xn--nding-jua/XFBAPE/SAMD/SAMD.h

const char* versionstring = "v3.1.4";
const char compile_date[] = __DATE__ " " __TIME__;

// the following defines will overwrite the standard arduino-defines from https://github.com/arduino/ArduinoCore-samd/blob/84c09b3265e2a8b548a29b141f0c9281b1baf154/variants/mkrvidor4000/variant.h
// this is only nescessary, if SAMD21 should transmit audio-data to FPGA. At the moment only ESP32 transmits audio-data
//#define I2S_INTERFACES_COUNT 1 // SAMD21 has two interfaces
//#define I2S_DEVICE 0 // select if I2S device 0 or 1
//#define I2S_CLOCK_GENERATOR 3 // select the correct clock for I2S-interface
//#define PIN_I2S_SD 21 // pin for SerialData (= A6)
//#define PIN_I2S_SCK 02 // pin for bit-clock (= D2)
//#define PIN_I2S_FS 03 // pin for FrameSelect / Wordclock (= D3)

// configure this software
#define USE_DISPLAY             0      // enables support for SSD1308 display connected to I2C
#define USE_MACKIE_MCU          1      // support for MackieMCU via MIDI
#define USE_ALL_MACKIE_FEATURES 0      // enable support for LED-rings, master-fader and 7-seg.-displays (all not supported by X32)
#define USE_XREMOTE             1      // support for XEdit via Ethernet
#define XREMOTE_DEVICE          "X32"  // XEdit will check this value and display the related picture
#define XREMOTE_FW_VER          "4.13" // XEdit will check this version
#define USE_XTOUCH              1      // support for XTouch via Ethernet
#define XTOUCH_COUNT            2      // number of supported XTouch-Devices
#define XTOUCH_COLOR            7      // color to init the channel: 0=BLACK, 1=RED, 2=GREEN, 3=YELLOW, 4=BLUE, 5=PINK, 6=CYAN, 7=WHITE (add 64 to invert)
#define XTOUCH_COLOR_DMX        3      // color to init the channel: 0=BLACK, 1=RED, 2=GREEN, 3=YELLOW, 4=BLUE, 5=PINK, 6=CYAN, 7=WHITE (add 64 to invert)

// includes for FPGA
#include <wiring_private.h>
#include "jtag.h"
#include "fpga.h"
#include <Ethernet.h>
#if USE_XTOUCH == 1
  #include <EthernetUdp.h>
#endif
#include <SPI.h>
#include "Ticker.h"

#if USE_MACKIE_MCU == 1
  #include <MIDI.h>
#endif

// definitions for I2C EEPROM
#include "Wire.h"
#include "I2C_eeprom.h"
#define EEPROM_Address 0x50

/*
Arduino SAMD21 SERCOM usage:
SERCOM0: I2C      <- Display
SERCOM1: SPI      <- W5500 Ethernet
SERCOM2: SPI1     <- unused
SERCOM3: Serial2  <- NINA
SERCOM4: unused (Pins 4/5)
SERCOM5: unused (Pins 16/17)

SerialUSB: USB
Serial1:   X32
*/
#define SerialX32 Serial1
#define SerialNina Serial2

// includes for Serial2 to communicate with NINA. As Serial2 is not within the scope of Arduino,
// we have to create it using the SERCOM-system of the SAMD21
#define PIN_SERIAL2_TX       (0ul)                // Pin description number for PIO_SERCOM on D0
#define PIN_SERIAL2_RX       (1ul)                // Pin description number for PIO_SERCOM on D1
#define PAD_SERIAL2_TX       (UART_TX_PAD_0)      // SERCOM pad 0 TX
#define PAD_SERIAL2_RX       (SERCOM_RX_PAD_1)    // SERCOM pad 1 RX
Uart Serial2(&sercom3, PIN_SERIAL2_RX, PIN_SERIAL2_TX, PAD_SERIAL2_RX, PAD_SERIAL2_TX);

#if USE_MACKIE_MCU == 1
  // includes for Serial3 to communicate with MIDI. As Serial3 is not within the scope of Arduino,
  // we have to create it using the SERCOM-system of the SAMD21
  #define PIN_SERIAL3_TX       (4ul)                // Pin description number for PIO_SERCOM
  #define PIN_SERIAL3_RX       (5ul)                // Pin description number for PIO_SERCOM
  #define PAD_SERIAL3_TX       (UART_TX_PAD_2)      // SERCOM pad 2 TX
  #define PAD_SERIAL3_RX       (SERCOM_RX_PAD_3)    // SERCOM pad 3 RX
  Uart Serial3(&sercom4, PIN_SERIAL3_RX, PIN_SERIAL3_TX, PAD_SERIAL3_RX, PAD_SERIAL3_TX);
  MIDI_CREATE_INSTANCE(HardwareSerial, Serial3, MIDI);
#endif

/*
#define PIN_SERIAL4_TX       (16ul)                // Pin description number for PIO_SERCOM
#define PIN_SERIAL4_RX       (17ul)                // Pin description number for PIO_SERCOM
#define PAD_SERIAL4_TX       (UART_TX_PAD_0)      // SERCOM pad 0 TX
#define PAD_SERIAL4_RX       (SERCOM_RX_PAD_1)    // SERCOM pad 1 RX
Uart Serial4(&sercom5, PIN_SERIAL4_RX, PIN_SERIAL4_TX, PAD_SERIAL4_RX, PAD_SERIAL4_TX);
*/

bool passthroughNINA = false;
bool passthroughNINADebug = false;
#define X32_RINGBUF_LEN 32 //longest command seems to be 22 chars
uint8_t x32RingBuffer[X32_RINGBUF_LEN];
uint16_t x32RingBufferPointer = 0;
uint8_t x32AliveCounter = 59; // preload to 5 seconds (for ticker with 85ms)
uint8_t x32StartupCounter = 100; // 10 Sekunden
String x32AliveCommand = "*8BE#";
bool x32Playback = false;
bool x32Debug = false;
uint8_t x32NumberOfCards = 2;
uint8_t x32currentCardSelection = 0;
uint32_t x32CardSize[2] = {31163136, 15581568}; // one 32GB and one 16GB

struct{ // don't change order of struct! Just add variables or replace with same size!!!
  uint16_t Version = 0;
  IPAddress ip;
  IPAddress xtouchip[XTOUCH_COUNT];
} eeprom_config;

struct{
  uint8_t mac[6] = {0xDE, 0xAD, 0xBE, 0xEF, 0xFE, 0xED};
} config;
I2C_eeprom eeprom(EEPROM_Address, I2C_DEVICESIZE_24LC16);

// Ethernet-objects
EthernetServer server(80);
EthernetServer cmdserver(5025);

#if USE_DISPLAY == 1
  #include "Wire.h"

  // includes for display
  #include "Bitmaps.h"
  #include <Adafruit_GFX.h>
  #include <Adafruit_SSD1306.h>
  #define SCREEN_WIDTH 128 // OLED display width, in pixels
  #define SCREEN_HEIGHT 64 // OLED display height, in pixels
  #define OLED_RESET     -1 // Reset pin # (or -1 if sharing Arduino reset pin)
  #define SCREEN_ADDRESS 0x3C // this address does not fit to the address on the PCB!!!
  Adafruit_SSD1306 display(SCREEN_WIDTH, SCREEN_HEIGHT, &Wire, OLED_RESET);
  uint8_t currentDisplayLine = 0;
#endif

String TOC;
uint8_t tocEntries = 3;
uint8_t tocCounter = 0;

struct {
  String title = "Standby...";
  uint8_t currentTrackNumber;
  uint32_t time;
  uint32_t duration;
  uint8_t progress;
  float volumeMain;
  uint8_t balanceMain;
  float volumeSub;
  float volumeCard;
  float volumeBt;
  float volumeCh[32] = {-48.0f, -48.0f, -48.0f, -48.0f, -48.0f, -48.0f, -48.0f, -48.0f, -48.0f, -48.0f, -48.0f, -48.0f, -48.0f, -48.0f, -48.0f, -48.0f, -48.0f, -48.0f, -48.0f, -48.0f, -48.0f, -48.0f, -48.0f, -48.0f, -48.0f, -48.0f, -48.0f, -48.0f, -48.0f, -48.0f, -48.0f, -48.0f};
  uint8_t balanceCh[32] = {50, 50, 50, 50, 50, 50, 50, 50, 50, 50, 50, 50, 50, 50, 50, 50, 50, 50, 50, 50, 50, 50, 50, 50, 50, 50, 50, 50, 50, 50, 50, 50};
  uint8_t vuMeterCh[32];
  uint8_t audioStatusInfo;

  String MainCtrlVersion;
  String FPGAVersion;
}playerinfo;

// some defines for NINA update mode
#define NINA_PIO27 11
#define NINA_RESET_N 31
unsigned long baud = 115200;
int rts = -1;
int dtr = -1;
bool firmwareUpdateMode = false;
uint8_t ledCounter = 10; // 500ms

// general variables
uint32_t refreshCounter = 0;

#if USE_MACKIE_MCU == 1 || USE_XTOUCH == 1
  uint8_t mackieUpdateCounter = 3; // 300ms update-rate
  bool mackieDmxMode = false;

  struct sMackieMCU_Channel{
    uint16_t faderPosition = 0; // 0...16383
    uint8_t encoderValue = 128; // 0..255 -> 0..12
    uint8_t rec = 0; // 0=OFF, 1=FLASHING, 127=ON (function unused at the moment)
    uint8_t solo = 0; // 0=OFF, 1=FLASHING, 127=ON
    uint8_t mute = 0; // 0=OFF, 1=FLASHING, 127=ON
    uint8_t select = 0; // 0=OFF, 1=FLASHING, 127=ON (function unused at the moment)
    String name;
    uint8_t color = XTOUCH_COLOR; // init the color with desired color for audio-channels (dmx-channels are set in setup())
  };

  struct sMackieMCU_ChannelHW{
    uint16_t faderPositionHW = 0; // 0...16383
    bool faderTouched = false;
    bool faderNeedsUpdate = false;
    uint8_t meterLevel; // 0...12 for Mackie, 0..8 for X-Touch
    uint8_t showValueCounter = 0; // show value for x seconds as counter is at 100ms
  };

  struct {
    uint8_t channelOffset = 0; // runs from 0 to 24
    uint16_t channelOffsetDmx = 0; // runs from 0 to 504
    bool forceUpdate = false;
    sMackieMCU_ChannelHW hardwareChannel[8];
    sMackieMCU_ChannelHW hardwareMainfader;
    sMackieMCU_Channel channel[33]; // values for audio-control
    sMackieMCU_Channel channelDmx[513]; // values for DMX-Control
    uint8_t jogDialValue;
    uint8_t jogDialValueDmx;
  }MackieMCU;
#endif

#if USE_XTOUCH == 1
  EthernetUDP XCtlUdp[XTOUCH_COUNT];
  uint8_t XCtl_UpdateCounter = 4;
  uint16_t XCtlWatchdogCounter[XTOUCH_COUNT];

  uint8_t XCtl_Probe[8] = {0xF0, 0x00, 0x20, 0x32, 0x58, 0x54, 0x00, 0xF7};
  uint8_t XCtl_ProbeResponse[8] = {0xF0, 0x00, 0x20, 0x32, 0x58, 0x54, 0x01, 0xF7};
  uint8_t XCtl_ProbeB[18] = {0xF0, 0x00, 0x00, 0x66, 0x58, 0x01, 0x30, 0x31, 0x35, 0x36, 0x34, 0x30, 0x36, 0x36, 0x37, 0x34, 0x30, 0xF7};
  uint8_t XCtl_ProbeC[18] = {0xF0, 0x00, 0x00, 0x66, 0x58, 0x01, 0x30, 0x31, 0x35, 0x36, 0x34, 0x30, 0x36, 0x33, 0x44, 0x35, 0x36, 0xF7};
  uint8_t XCtl_IdlePacket[7] = {0xF0, 0x00, 0x00, 0x66, 0x14, 0x00, 0xF7};

  struct sXCtl{
    IPAddress ip;
    bool online = false;
    uint8_t channelOffset = 0;
    uint16_t channelOffsetDmx = 0; // 0...504
    bool forceUpdate = false;
    sMackieMCU_ChannelHW hardwareChannel[8];
    sMackieMCU_ChannelHW hardwareMainfader;
    bool showNames = true;
    bool dmxMode = false;
    uint8_t jogDialValue = 0;
    uint8_t jogDialValueDmx = 0;
    char segmentDisplay[12];
    uint8_t buttonLightOn[103];
  }XCtl[XTOUCH_COUNT];
#endif

#if USE_XREMOTE == 1
  EthernetUDP xremoteUdp;
  uint8_t xremoteUpdateCounter = 1;
  char xremote_TxMessage[350]; // the largest binary blob will take up to 20+(70+1))*4 bytes = 408 bytes

  typedef union 
  {
      uint32_t u32;
      int32_t s32;
      uint16_t u16[2];
      int16_t s16[2];
      uint8_t u8[4];
      int8_t s8[4];
      float   f;
  }data_32b;

  char xremote_cmd_info[4]   = {'/', 'i', 'n', 'f'};
  char xremote_cmd_xinfo[4]   = {'/', 'x', 'i', 'n'};
  char xremote_cmd_status[4] = {'/', 's', 't', 'a'};
  char xremote_cmd_xremote[4]   = {'/', 'x', 'r', 'e'};
  char xremote_cmd_unsubscribe[4]   = {'/', 'u', 'n', 's'};
  char xremote_cmd_channel[4]   = {'/', 'c', 'h', '/'};
  char xremote_cmd_main[4]   = {'/', 'm', 'a', 'i'};
  char xremote_cmd_stat[4]   = {'/', '-', 's', 't'};
#endif
