xn--nding-jua/XFBAPE/FPGA/vu_meter_32ch.vhd

-- vu-meter
-- (c) 2023 Dr.-Ing. Christian Noeding
-- christian@noeding-online.de
-- Released under GNU General Public License v3
-- Source: https://www.github.com/xn--nding-jua/Audioplayer
--
-- This file converts 24-bit signed audio-data into a 8-bit unsigned VU-meter between -6dBfs and -78dBfs

library IEEE;
use IEEE.STD_LOGIC_1164.ALL;
use ieee.numeric_std.all;

entity vu_meter_32ch is
	port (
		ch1_in		:	in signed(23 downto 0) := (others=>'0');
		ch2_in		:	in signed(23 downto 0) := (others=>'0');
		ch3_in		:	in signed(23 downto 0) := (others=>'0');
		ch4_in		:	in signed(23 downto 0) := (others=>'0');
		ch5_in		:	in signed(23 downto 0) := (others=>'0');
		ch6_in		:	in signed(23 downto 0) := (others=>'0');
		ch7_in		:	in signed(23 downto 0) := (others=>'0');
		ch8_in		:	in signed(23 downto 0) := (others=>'0');
		ch9_in		:	in signed(23 downto 0) := (others=>'0');
		ch10_in		:	in signed(23 downto 0) := (others=>'0');
		ch11_in		:	in signed(23 downto 0) := (others=>'0');
		ch12_in		:	in signed(23 downto 0) := (others=>'0');
		ch13_in		:	in signed(23 downto 0) := (others=>'0');
		ch14_in		:	in signed(23 downto 0) := (others=>'0');
		ch15_in		:	in signed(23 downto 0) := (others=>'0');
		ch16_in		:	in signed(23 downto 0) := (others=>'0');
		ch17_in		:	in signed(23 downto 0) := (others=>'0');
		ch18_in		:	in signed(23 downto 0) := (others=>'0');
		ch19_in		:	in signed(23 downto 0) := (others=>'0');
		ch20_in		:	in signed(23 downto 0) := (others=>'0');
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
			vu_ch15 <= ch15(20) & ch15(17) & ch15(15) & ch15(13) & ch15(12) & ch15(11) & ch15(10) & ch15(9);
			vu_ch16 <= ch16(20) & ch16(17) & ch16(15) & ch16(13) & ch16(12) & ch16(11) & ch16(10) & ch16(9);
			vu_ch17 <= ch17(20) & ch17(17) & ch17(15) & ch17(13) & ch17(12) & ch17(11) & ch17(10) & ch17(9);
			vu_ch18 <= ch18(20) & ch18(17) & ch18(15) & ch18(13) & ch18(12) & ch18(11) & ch18(10) & ch18(9);
			vu_ch19 <= ch19(20) & ch19(17) & ch19(15) & ch19(13) & ch19(12) & ch19(11) & ch19(10) & ch19(9);
			vu_ch20 <= ch20(20) & ch20(17) & ch20(15) & ch20(13) & ch20(12) & ch20(11) & ch20(10) & ch20(9);
			vu_ch21 <= ch21(20) & ch21(17) & ch21(15) & ch21(13) & ch21(12) & ch21(11) & ch21(10) & ch21(9);
			vu_ch22 <= ch22(20) & ch22(17) & ch22(15) & ch22(13) & ch22(12) & ch22(11) & ch22(10) & ch22(9);
			vu_ch23 <= ch23(20) & ch23(17) & ch23(15) & ch23(13) & ch23(12) & ch23(11) & ch23(10) & ch23(9);
			vu_ch24 <= ch24(20) & ch24(17) & ch24(15) & ch24(13) & ch24(12) & ch24(11) & ch24(10) & ch24(9);
			vu_ch25 <= ch25(20) & ch25(17) & ch25(15) & ch25(13) & ch25(12) & ch25(11) & ch25(10) & ch25(9);
			vu_ch26 <= ch26(20) & ch26(17) & ch26(15) & ch26(13) & ch26(12) & ch26(11) & ch26(10) & ch26(9);
			vu_ch27 <= ch27(20) & ch27(17) & ch27(15) & ch27(13) & ch27(12) & ch27(11) & ch27(10) & ch27(9);
			vu_ch28 <= ch28(20) & ch28(17) & ch28(15) & ch28(13) & ch28(12) & ch28(11) & ch28(10) & ch28(9);
			vu_ch29 <= ch29(20) & ch29(17) & ch29(15) & ch29(13) & ch29(12) & ch29(11) & ch29(10) & ch29(9);
			vu_ch30 <= ch30(20) & ch30(17) & ch30(15) & ch30(13) & ch30(12) & ch30(11) & ch30(10) & ch30(9);
			vu_ch31 <= ch31(20) & ch31(17) & ch31(15) & ch31(13) & ch31(12) & ch31(11) & ch31(10) & ch31(9);
			vu_ch32 <= ch32(20) & ch32(17) & ch32(15) & ch32(13) & ch32(12) & ch32(11) & ch32(10) & ch32(9);
		end if;
	end process;
end Behavioral;
