xn--nding-jua/XFBAPE/FPGA/compressor_stereosub.vhd

-- Compressor/Limiter Filter
-- (c) 2023 Dr.-Ing. Christian Noeding
-- christian@noeding-online.de
-- Released under GNU General Public License v3
-- Source: https://www.github.com/xn--nding-jua/xfbape
-- Original Source: https://github.com/YetAnotherElectronicsChannel/FPGA-Audio-IIR
--
-- This file contains a compressor/limiter that will set the output to a specific
-- maximum gain-value depending on a specific maximum threshold.
-- The gain-change will be filtered by a first-order low-pass filter
-- for which two coefficients (for attack and release) have to be set
--
-- It is same as compressor_stereo.vhd but with additional subwoofer-channel. The
-- combined version saves some logic-elements as we are using a single divider

-- Online-Calculation of Filter-Coefficients: https://www.earlevel.com/main/2021/09/02/biquad-calculator-v3

library ieee;
use ieee.std_logic_1164.all;
use ieee.std_logic_unsigned.all; 
use ieee.numeric_std.all; -- lib for unsigned and signed

entity compressor_stereosub is
	generic (
		bit_width		:	natural range 16 to 48 := 24;
		threshold_bit_width	:	natural range 16 to 48 := 24
	);
	port (
		clk				:	in std_logic := '0';

		sample_l_in		:	in signed(bit_width - 1 downto 0) := (others=>'0');
		sample_r_in		:	in signed(bit_width - 1 downto 0) := (others=>'0');
		sample_sub_in	:	in signed(bit_width - 1 downto 0) := (others=>'0');
		sync_in			:	in std_logic := '0';
		rst				:	in std_logic := '0';
		
		-- setup-input for left/right-compressor
		threshold_lr	:	in unsigned(threshold_bit_width - 1 downto 0) := (others=>'0'); -- threshold with bitdepth of sample, that will be used to check the audio-level (between 0 and 8388608)
		ratio_lr			:	in unsigned(7 downto 0) := (others=>'0'); -- ratio of gain-reduction (0=1:1, 1=2:1, 2=4:1, 3=8:1, 4=16:1, 5=32:1, 6=64:1, ...)
		makeup_lr		:	in unsigned(7 downto 0) := (others=>'0'); -- makeup-gain. (0=x1, 1=x2, 2=x4, 3=x8, 4=x16, 5=x32, 6=x64, 7=x128, 8=x256, ...)
		coeff_attack_lr	:	in signed(15 downto 0); -- Q15-format, 1 bit sign, 0 bit for integer-part, 15 bit for fraction-part
		hold_ticks_lr	:	in unsigned(15 downto 0) := (others=>'0'); -- 16 bit value for hold_counter = 0...65535/48000 [0...1365ms]
		coeff_release_lr	:	in signed(15 downto 0); -- Q15-format, 1 bit sign, 0 bit for integer-part, 15 bit for fraction-part
		
		-- setup-input for subwoofer-compressor
		threshold_sub	:	in unsigned(threshold_bit_width - 1 downto 0) := (others=>'0'); -- threshold with bitdepth of sample, that will be used to check the audio-level (between 0 and 8388608)
		ratio_sub		:	in unsigned(7 downto 0) := (others=>'0'); -- ratio of gain-reduction (0=1:1, 1=2:1, 2=4:1, 3=8:1, 4=16:1, 5=32:1, 6=64:1, ...)
		makeup_sub		:	in unsigned(7 downto 0) := (others=>'0'); -- makeup-gain. (0=x1, 1=x2, 2=x4, 3=x8, 4=x16, 5=x32, 6=x64, 7=x128, 8=x256, ...)
		coeff_attack_sub	:	in signed(15 downto 0); -- Q15-format, 1 bit sign, 0 bit for integer-part, 15 bit for fraction-part
		hold_ticks_sub	:	in unsigned(15 downto 0) := (others=>'0'); -- 16 bit value for hold_counter = 0...65535/48000 [0...1365ms]
		coeff_release_sub	:	in signed(15 downto 0); -- Q15-format, 1 bit sign, 0 bit for integer-part, 15 bit for fraction-part

		sample_l_out	:	out signed(bit_width - 1 downto 0) := (others=>'0');
		sample_r_out	:	out signed(bit_width - 1 downto 0) := (others=>'0');
		sample_sub_out	:	out signed(bit_width - 1 downto 0) := (others=>'0');
		sync_out			:	out std_logic := '0';
		comp_lr_out		:	out std_logic := '0';
		comp_sub_out	:	out std_logic := '0'
	);
end compressor_stereosub;

architecture rtl of compressor_stereosub is
	-- signals for the state-machines
	signal s_SM_Main	:	natural range 0 to 18 := 0;
	type t_SM_Effect is (s_Idle, s_Attack, s_Active, s_Hold, s_Release);
	signal s_SM_Effect_lr 	: t_SM_Effect := s_Release; -- start in release mode
	signal s_SM_Effect_sub 	: t_SM_Effect := s_Release; -- start in release mode

	-- signals for processing
	signal sample_l	:	signed(bit_width - 1 downto 0) := (others=>'0');
	signal sample_r	:	signed(bit_width - 1 downto 0) := (others=>'0');
	signal sample_sub	:	signed(bit_width - 1 downto 0) := (others=>'0');
	signal sample_tmp	:	signed(bit_width - 1 downto 0) := (others=>'0');
	signal coeff_lr	:	signed(15 downto 0); -- Q15-format, 1 bit for sign, 0 bit for integer-part, 15 bit for fraction-part
	signal coeff_sub	:	signed(15 downto 0); -- Q15-format, 1 bit for sign, 0 bit for integer-part, 15 bit for fraction-part
	
	signal gain_set_lr	:	unsigned(bit_width - 1 downto 0) := (others=>'0'); -- target-value that is calculated
	signal gain_set_sub	:	unsigned(bit_width - 1 downto 0) := (others=>'0'); -- target-value that is calculated
	signal gain_lr		:	unsigned(22 downto 0) := (others=>'0'); -- unsigned Q15-format, that will be used for current gain and holds value as gain_z1 for next step
	signal gain_sub	:	unsigned(22 downto 0) := (others=>'0'); -- unsigned Q15-format, that will be used for current gain and holds value as gain_z1 for next step
	
	signal hold_counter_lr	:	unsigned(15 downto 0) := (others=>'0'); -- unsigned 16 bit counter for hold_counter = 0...1365ms
	signal hold_counter_sub	:	unsigned(15 downto 0) := (others=>'0'); -- unsigned 16 bit counter for hold_counter = 0...1365ms

	--signals for multiplier
	signal mult_in_a	:	signed(bit_width - 1 downto 0) := (others=>'0');
	signal mult_in_b	:	signed(15 downto 0) := (others=>'0');
	signal mult_out	:	signed((bit_width + 16) - 1 downto 0) := (others=>'0');

	-- signals for divider
	signal div_start		:	std_logic;
	signal div_dividend	:	unsigned(bit_width - 1 downto 0) := (others=>'0'); -- temporary value for gain_set
	signal div_busy		:	std_logic;
	signal div_quotient	:	unsigned(bit_width - 1 downto 0) := (others=>'0');
	-- copy inputs/outputs from Divider-entity
	component divider is
		generic (
			bit_width	: natural range 4 to 48 := 24
		);
		port (
			clk			: in   std_logic;
			start			: in   std_logic;
			dividend		: in   unsigned(bit_width - 1 downto 0);
			divisor		: in   unsigned(bit_width - 1 downto 0);
			quotient		: out  unsigned(bit_width - 1 downto 0);
			remainder	: out  unsigned(bit_width - 1 downto 0);
			busy			: out  std_logic
		);
	end component;
begin
	-- multiplier
	process(mult_in_a, mult_in_b)
	begin
		mult_out <= mult_in_a * mult_in_b;
	end process;
	
	-- divider
	div : divider
		generic map(
			bit_width => bit_width
		)
		port map(
			clk => clk,
			start => div_start,
			dividend => div_dividend,
			divisor => unsigned(sample_tmp), -- sample_tmp contains only the abs()-value of sample. So its OK to cast to unsigned
			quotient => div_quotient,
			remainder => open,
			busy => div_busy
		);

	process(clk)
		variable effect_triggered_lr : std_logic := '0';
		variable effect_triggered_sub : std_logic := '0';
	begin
		if rising_edge(clk) then
			if (rst = '1') then
				-- reset compressor for left/right
				effect_triggered_lr := '0';
				gain_set_lr <= to_unsigned(255, gain_set_lr'length);
				coeff_lr <= coeff_release_lr;
				s_SM_Effect_lr <= s_Idle;
				
				-- reset compressor for subwoofer
				effect_triggered_sub := '0';
				gain_set_sub <= to_unsigned(255, gain_set_sub'length);
				coeff_sub <= coeff_release_sub;
				s_SM_Effect_sub <= s_Idle;
				
				-- reset outputs and statemachine
				sync_out <= '0';
				s_SM_Main <= 0;
			end if;
		
			if (sync_in = '1' and s_SM_Main = 0) then
				-- we are receiving a new sample
				
				-- copy sample to internal signal
				sample_l <= sample_l_in;
				sample_r <= sample_r_in;
				sample_sub <= sample_sub_in;

				-- create a processing-sample containing the loudest signal
				if (unsigned(abs(sample_l_in)) > unsigned(abs(sample_r_in))) then
					-- left is louder than right
					sample_tmp <= abs(sample_l_in);

					-- check if we have to reduce gain
					if (unsigned(abs(sample_l_in)) > threshold_lr) then
						effect_triggered_lr := '1';
					else
						effect_triggered_lr := '0';
					end if;
				else
					-- right is louder than left
					sample_tmp <= abs(sample_r_in);
					
					-- check if we have to reduce gain
					if (unsigned(abs(sample_r_in)) > threshold_lr) then
						effect_triggered_lr := '1';
					else
						effect_triggered_lr := '0';
					end if;
				end if;

				s_SM_Main <= s_SM_Main + 1; -- go into next state
			elsif (s_SM_Main = 1) then
				-- precalculate a temporary value for gain_set
				-- overshoot = sample_tmp - threshold
				-- output = overshoot / ratio + threshold
				-- gain = (output / sample_tmp) * 256
				-- we will calculate the divisor including factor of 256:
				div_dividend <= shift_left(resize((shift_right(unsigned(sample_tmp) - threshold_lr, to_integer(ratio_lr)) + threshold_lr), div_dividend'length), 8) - 5; -- division has limited precision, so we will keep a larger distance away from 256 to mitigate overflow
				-- sample_tmp is already mapped to divider as divisor
				
				-- start divider
				div_start <= '1';
				
				s_SM_Main <= s_SM_Main + 1; -- go into next state
			elsif (s_SM_Main = 2) then
				-- one wait-state

				-- set divider-start to 0 for next cycle
				div_start <= '0';

				s_SM_Main <= s_SM_Main + 1; -- go into next state
			elsif (s_SM_Main = 3 and div_busy = '0') then
				-- check state of Effect-Statemachine
				case s_SM_Effect_lr is
					when s_Idle =>
						-- Effect is idle (off)
						
						-- check level for entering attack-state
						if (effect_triggered_lr = '1') then
							s_SM_Effect_lr <= s_Attack;
						end if;
					when s_Attack =>
						-- Effect entered attack-state
						
						-- we are limiting with a specific ratio: 0=1:1, 1=2:1, 2=4:1, 3=8:1, 4=16:1, 5=32:1, 6=64:1, ..., 24=oo:1=Limiter
						-- general equation is: output = (input - threshold)/ratio + threshold
						-- equation for desired gain is: gain = output / input

						--gain_set_lr <= to_unsigned(32, gain_set_lr'length); -- for debugging: set volume during compression to 12.5% (=32/256)
						gain_set_lr <= div_quotient; -- take the desired gain from division
						coeff_lr <= coeff_attack_lr;
						
						-- go directly into on-state
						-- we could add a attack-state-counter here, but the wait-time
						-- will depend on coefficients, so keep it simple
						s_SM_Effect_lr <= s_Active;
					when s_Active =>
						-- Effect is in on-state

						if (effect_triggered_lr = '1') then
							-- value is still above threshold -> update gain if below last gain
							if (div_quotient < gain_set_lr) then
								-- we have to reduce gain even more
								gain_set_lr <= div_quotient; -- take the desired gain from division
							end if;
						else
							-- we are below the threshold
							
							-- load counter and enter release-hold-state
							hold_counter_lr <= hold_ticks_lr;
							s_SM_Effect_lr <= s_Hold;
						end if;
					when s_Hold =>
						-- Effect is in hold-state before release

						if (effect_triggered_lr = '1') then
							-- value is above threshold again -> re-enter on-State
							s_SM_Effect_lr <= s_Active;
						else
							-- we are below the threshold
							
							-- check hold_counter
							if (hold_counter_lr = 0) then
								-- we reached end of hold -> enter release-state
								s_SM_Effect_lr <= s_Release;
							else
								-- we still have to stay in hold
								-- decrement hold-counter
								hold_counter_lr <= hold_counter_lr - 1;
							end if;
						end if;
					when s_Release =>
						-- Effect entered release-state
						
						-- set desired gain-level to 100%
						-- set release-coefficient for LP-filter
						-- gain itself will be set via low-pass-filter down below
						gain_set_lr <= to_unsigned(255, gain_set_lr'length);
						coeff_lr <= coeff_release_lr;
						
						-- go directly into idle-state (TODO: we could add a release-state-counter here, but the wait-time will depend on coefficients)
						s_SM_Effect_lr <= s_Idle;
				end case;
				
				s_SM_Main <= s_SM_Main + 1; -- go into next state
			elsif (s_SM_Main = 4) then
				-- now calculate low-pass-filter: gain = coeff * gain_z1 - coeff * gain + gain

				-- first, calculate the front part of filter-equation: part1 = coeff * gain_z1

				-- load multiplier
				mult_in_a <= resize(signed("0" & std_logic_vector(gain_lr)), mult_in_a'length); -- gain-value (from last sample = z^-1) is in unsigned Q8.15-format -> convert to signed Q8.15
				mult_in_b <= coeff_lr; -- coefficient in Q0.15-format

				s_SM_Main <= s_SM_Main + 1; -- go into next state
			elsif (s_SM_Main = 5) then
				-- store first part and calculate next part of filter: coeff * gain
			
				-- convert resulting Q8.30 back to unsigned Q8.15 by removing/ignoring least-significant 15 bits
				gain_lr <= unsigned(std_logic_vector(mult_out)(22+15 downto 0+15)); -- we ignore the signed-bit here, as gain is unsigned
				
				-- load multiplier
				mult_in_a <= resize(signed("0" & std_logic_vector(gain_set_lr)), mult_in_a'length); -- desired gain is in unsigned Q8.0-format -> convert to signed Q8.0
				mult_in_b <= coeff_lr; -- coefficient in Q0.15-format
				
				s_SM_Main <= s_SM_Main + 1; -- go into next state
			elsif (s_SM_Main = 6) then
				-- calculate full value: gain = coeff * gain_z1 - coeff * gain + gain 
				
				-- convert gain_set from unsigned Q8.0 to unsigned Q8.15
				-- convert multiplication-result (alpha*gain_set) from signed Q8.15 to unsigned Q8.15
				-- calc: (alpha*gain) + (gain_set - alpha*gain_set)
				
				gain_lr <= gain_lr + (resize(unsigned(std_logic_vector(gain_set_lr) & "000000000000000"), gain_lr'length) - unsigned(std_logic_vector(mult_out)(22 downto 0)));
				
				s_SM_Main <= s_SM_Main + 1; -- go into next state
			elsif (s_SM_Main = 7) then
				-- calculate the output signal
				
				-- load multiplier
				mult_in_a <= sample_l; -- audio-sample for left-channel
				mult_in_b <= signed("0" & std_logic_vector(gain_lr)(22 downto 8)); -- convert current gain-value from Q8.15 into Q8.7-format
				
				s_SM_Main <= s_SM_Main + 1;
			elsif (s_SM_Main = 8) then
				-- convert resulting signed Q8.7 back to Q8.0, divide by 256 and store sample into signal
				-- applying makeup-gain by bitshift to the left again
				sample_tmp <= resize(shift_right(mult_out, 8 + 7 - to_integer(makeup_lr)) , bit_width);

				-- load multiplier
				mult_in_a <= sample_r; -- audio-sample for right channel
				mult_in_b <= signed("0" & std_logic_vector(gain_lr)(22 downto 8)); -- convert current gain-value from Q8.15 into Q8.7-format
				
				s_SM_Main <= s_SM_Main + 1;
			elsif (s_SM_Main = 9) then
				-- set samples for left and right to output
				sample_l_out <= sample_tmp;
				sample_r_out <= resize(shift_right(mult_out, 8 + 7 - to_integer(makeup_lr)) , bit_width); -- convert resulting signed Q8.7 back to Q8.0, divide by 256 and output signal

				s_SM_Main <= s_SM_Main + 1;
			elsif (s_SM_Main = 10) then
				-- now calculate the compressor for the subwoofer-channel
			
				-- copy sample_sub to sample_tmp as this will be used as divisor
				sample_tmp <= abs(sample_sub);
			
				-- check if the effect is triggered
				if (unsigned(abs(sample_sub)) > threshold_sub) then
					effect_triggered_sub := '1';
				else
					effect_triggered_sub := '0';
				end if;

				s_SM_Main <= s_SM_Main + 1; -- go into next state
			elsif (s_SM_Main = 11) then
				-- precalculate a temporary value for gain_set
				-- overshoot = sample - threshold
				-- output = overshoot / ratio + threshold
				-- gain = (output / sample) * 256
				-- we will calculate the divisor including factor of 256:
				div_dividend <= shift_left(resize((shift_right(unsigned(sample_tmp) - threshold_sub, to_integer(ratio_sub)) + threshold_sub), div_dividend'length), 8) - 5; -- division has limited precision, so we will keep a larger distance away from 256 to mitigate overflow
				-- sample_tmp is already mapped to divider as divisor
				
				-- start divider
				div_start <= '1';

				s_SM_Main <= s_SM_Main + 1; -- go into next state
			elsif (s_SM_Main = 12 and div_busy = '0') then
				-- set divider-start to 0 for next cycle
				div_start <= '0';

				-- check state of Effect-Statemachine
				case s_SM_Effect_sub is
					when s_Idle =>
						-- Effect is idle (off)
						
						-- check level for entering attack-state
						if (effect_triggered_sub = '1') then
							s_SM_Effect_sub <= s_Attack;
						end if;
					when s_Attack =>
						-- Effect entered attack-state
						
						-- we are limiting with a specific ratio: 0=1:1, 1=2:1, 2=4:1, 3=8:1, 4=16:1, 5=32:1, 6=64:1, ..., 24=oo:1=Limiter
						-- general equation is: output = (input - threshold)/ratio + threshold
						-- equation for desired gain is: gain = output / input

						--gain_set <= to_unsigned(32, gain_set'length); -- for debugging: set volume during compression to 12.5% (=32/256)
						gain_set_sub <= div_quotient; -- take the desired gain from division
						coeff_sub <= coeff_attack_sub;
						
						-- go directly into on-state
						-- we could add a attack-state-counter here, but the wait-time
						-- will depend on coefficients, so keep it simple
						s_SM_Effect_sub <= s_Active;
					when s_Active =>
						-- Effect is in on-state

						if (effect_triggered_sub = '1') then
							-- value is still above threshold -> update gain if below last gain
							if (div_quotient < gain_set_sub) then
								-- we have to reduce gain even more
								gain_set_sub <= div_quotient; -- take the desired gain from division
							end if;
						else
							-- we are below the threshold
							
							-- load counter and enter release-hold-state
							hold_counter_sub <= hold_ticks_sub;
							s_SM_Effect_sub <= s_Hold;
						end if;
					when s_Hold =>
						-- Effect is in hold-state before release
						if (effect_triggered_sub = '1') then
							-- value is above threshold_sub again -> re-enter on-State
							s_SM_Effect_sub <= s_Active;
						else
							-- we are below the threshold_sub
							
							-- check hold_counter_sub
							if (hold_counter_sub = 0) then
								-- we reached end of hold -> enter release-state
								s_SM_Effect_sub <= s_Release;
							else
								-- we still have to stay in hold
								-- decrement hold-counter_sub
								hold_counter_sub <= hold_counter_sub - 1;
							end if;
						end if;
					when s_Release =>
						-- Effect entered release-state
						
						-- set desired gain-level to 100%
						-- set release-coefficient for LP-filter
						-- gain itself will be set via low-pass-filter down below
						gain_set_sub <= to_unsigned(255, gain_set_sub'length);
						coeff_sub <= coeff_release_sub;
						
						-- go directly into idle-state (TODO: we could add a release-state-counter here, but the wait-time will depend on coefficients)
						s_SM_Effect_sub <= s_Idle;
				end case;
				
				s_SM_Main <= s_SM_Main + 1; -- go into next state
			elsif (s_SM_Main = 13) then
				-- now calculate low-pass-filter: gain = coeff * gain_z1 - coeff * gain + gain

				-- first, calculate the front part of filter-equation: part1 = coeff * gain_z1

				-- load multiplier
				mult_in_a <= resize(signed("0" & std_logic_vector(gain_sub)), mult_in_a'length); -- gain-value (from last sample = z^-1) is in unsigned Q8.15-format -> convert to signed Q8.15
				mult_in_b <= coeff_sub; -- coefficient in Q0.15-format
				
				s_SM_Main <= s_SM_Main + 1; -- go into next state
			elsif (s_SM_Main = 14) then
				-- store first part and calculate next part of filter: coeff * gain
			
				-- convert resulting Q8.30 back to unsigned Q8.15 by removing/ignoring least-significant 15 bits
				gain_sub <= unsigned(std_logic_vector(mult_out)(22+15 downto 0+15)); -- we ignore the signed-bit here, as gain is unsigned
				
				-- load multiplier
				mult_in_a <= resize(signed("0" & std_logic_vector(gain_set_sub)), mult_in_a'length); -- desired gain is in unsigned Q8.0-format -> convert to signed Q8.0
				mult_in_b <= coeff_sub; -- coefficient in Q0.15-format
				
				s_SM_Main <= s_SM_Main + 1; -- go into next state
			elsif (s_SM_Main = 15) then
				-- calculate full value: gain = coeff * gain_z1 - coeff * gain + gain 
				
				-- convert gain_set from unsigned Q8.0 to unsigned Q8.15
				-- convert multiplication-result (alpha*gain_set) from signed Q8.15 to unsigned Q8.15
				-- calc: (alpha*gain) + (gain_set - alpha*gain_set)
				
				gain_sub <= gain_sub + (resize(unsigned(std_logic_vector(gain_set_sub) & "000000000000000"), gain_sub'length) - unsigned(std_logic_vector(mult_out)(22 downto 0)));
				
				s_SM_Main <= s_SM_Main + 1; -- go into next state
			elsif (s_SM_Main = 16) then
				-- calculate the output signal
				
				-- load multiplier
				mult_in_a <= sample_sub; -- audio-sample
				mult_in_b <= signed("0" & std_logic_vector(gain_sub)(22 downto 8)); -- convert current gain-value from Q8.15 into Q8.7-format
				
				s_SM_Main <= s_SM_Main + 1;
			elsif (s_SM_Main = 17) then
				-- convert resulting signed Q8.7 back to Q8.0 and set output, divide by 256 and output signal
				-- applying makeup-gain by bitshift to the left again
				sample_sub_out <= resize(shift_right(mult_out, 8 + 7 - to_integer(makeup_sub)) , bit_width);
				
				-- indicate, if we are compressing
				if (shift_right(gain_lr, 15) < 250) then
					comp_lr_out <= '1';
				else
					comp_lr_out <= '0';
				end if;
				if (shift_right(gain_sub, 15) < 250) then
					comp_sub_out <= '1';
				else
					comp_sub_out <= '0';
				end if;
				
				sync_out <= '1';
				
				s_SM_Main <= s_SM_Main + 1;
			elsif (s_SM_Main = 18) then
				-- cleanup and return to state 0
				sync_out <= '0';
				
				s_SM_Main <= 0;
			end if;
		end if;
	end process;
end rtl;
